fablabs-ch/wordclock/images/wiki/arduino_ide_board_selection.png

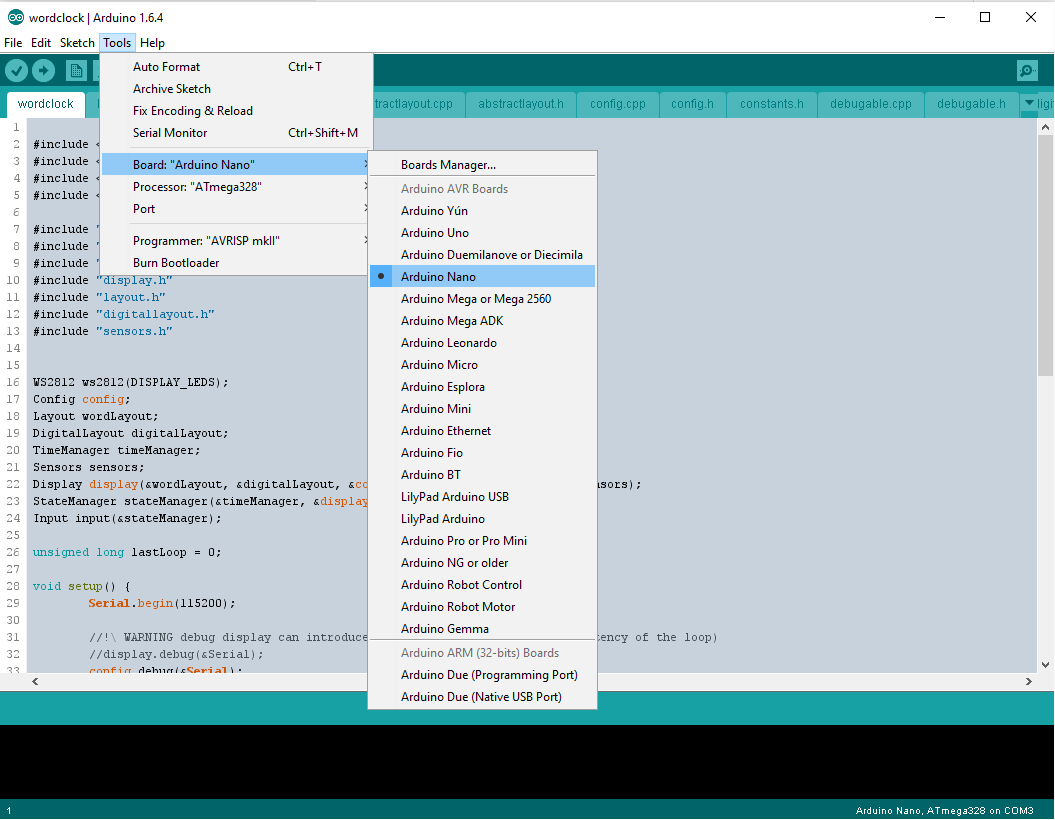
images/wiki/arduino_ide_board_selection.png
