fablabs-ch/wordclock/images/wordclockUpdatedFrench.JPG

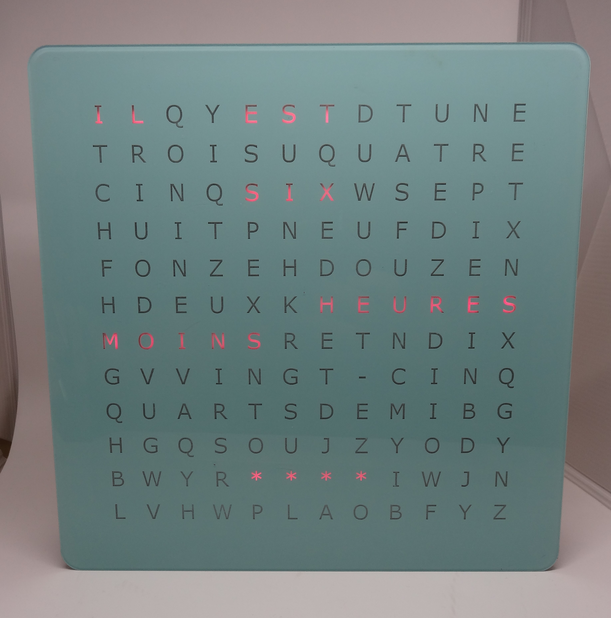
images/wordclockUpdatedFrench.JPG
