fablabs-ch/wordclock/hardware/electronic/pics/components.jpg

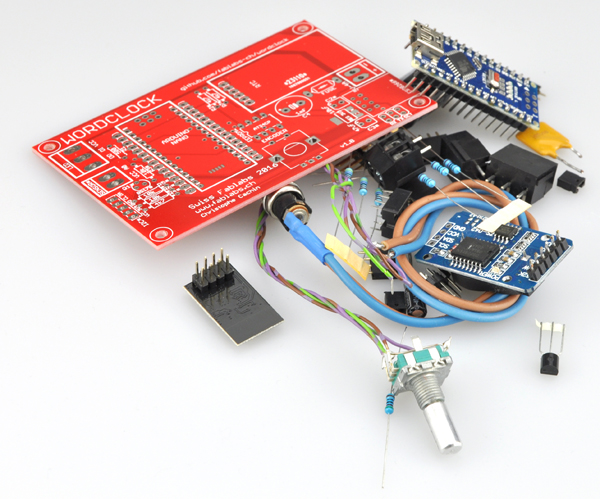
hardware/electronic/pics/components.jpg
