fablabs-ch/wordclock/hardware/box/WordClock_assembly.jpg

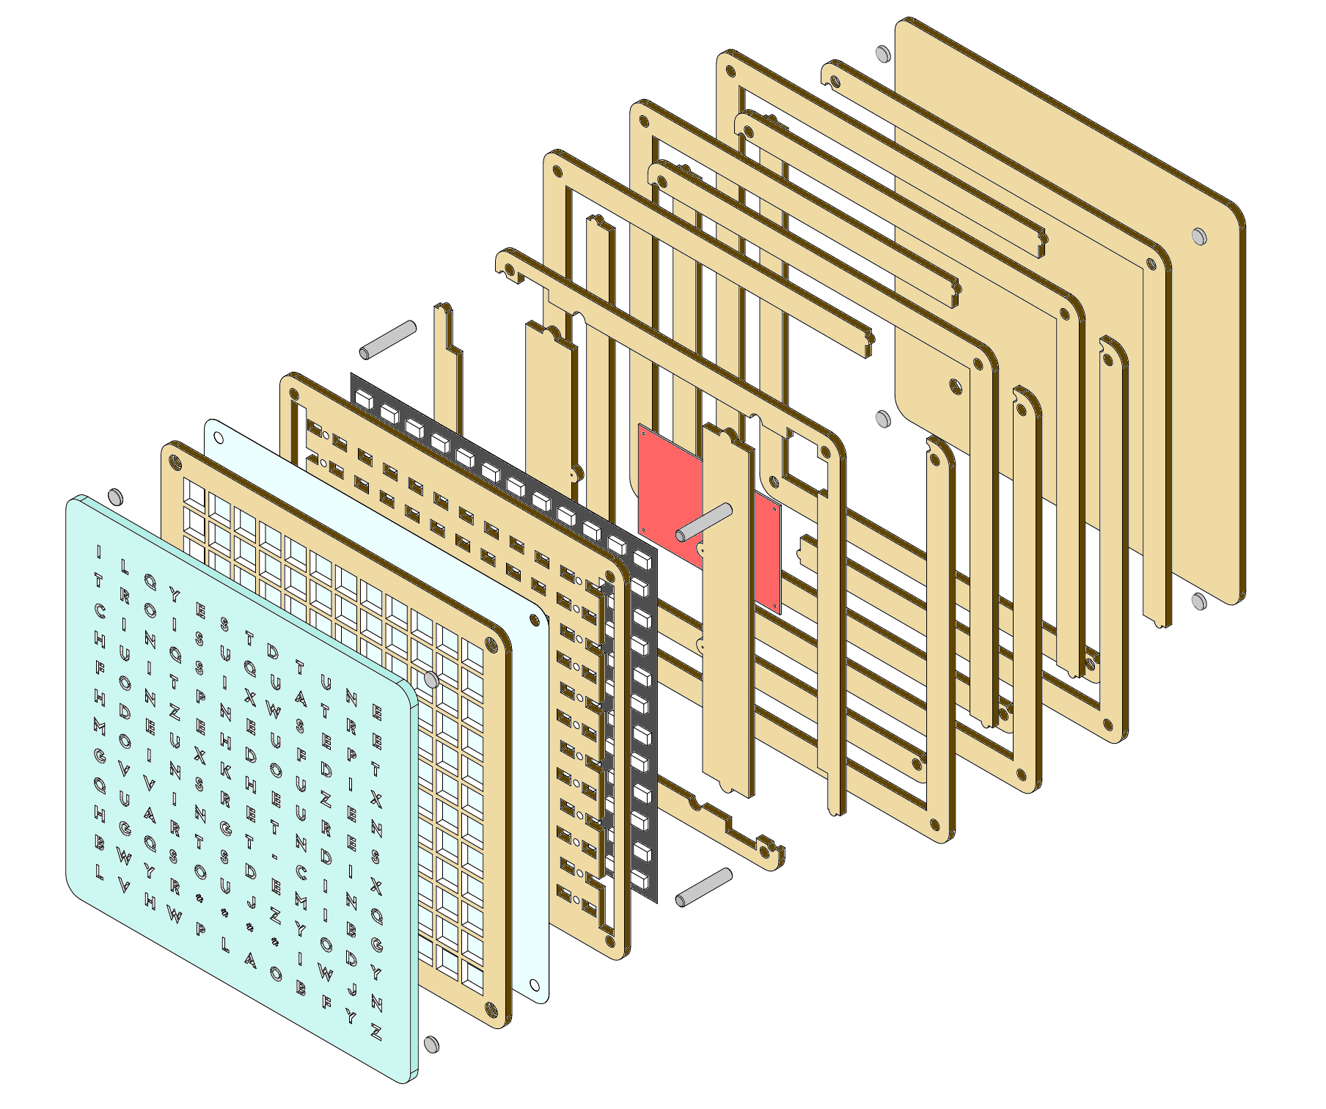
hardware/box/WordClock_assembly.jpg
