fablabs-ch/wordclock/software/wordclock/display.cpp

#include "display.h"

// #define ADD_LED(name) {int leds[] = {name};	this->addLedsOn(leds);}

Display::Display(AbstractLayout* wordLayout, AbstractLayout* digitalLayout, Config* config, TimeManager* timeManager, WS2812* ws2812, Sensors* sensors)
: wordLayout(wordLayout), digitalLayout(digitalLayout), config(config), timeManager(timeManager), leds(ws2812), sensors(sensors) {

	this->leds->setOutput(PIN_LED_STRIP);
	this->leds->setColorOrderRGB();
}

void Display::init() {
	this->draw();
	this->accNextDraw = 0;
}

void Display::loop(unsigned long dtMs) {
	this->accNextDraw += dtMs;

	bool blink = this->currentState == SET_MINUTE || this->currentState == SET_HOUR;
	if (blink) {
		int next = this->blinkOn ? 100 : 200;
		if (this->accNextDraw >= next) {
			if (this->blinkOn) {
				this->draw();
			} else {
				this->allLedsOff();
				this->writeLeds();
			}
			this->blinkOn = !this->blinkOn;
			this->accNextDraw = 0;
		}
	} else {
	    //watch for motion detection changes
	    if(this->wasMotionDetected != this->sensors->isMotionDetected()){
	        this->wasMotionDetected = this->sensors->isMotionDetected();
	        if(this->wasMotionDetected){
	            this->draw();
	        }else{
                 this->allLedsOff();
                 this->writeLeds();
            }
	    }

		if (this->accNextDraw >= DISPLAY_REFRESH_MS || this->sensors->bigChangeOccurs()) {
		    if(this->sensors->isMotionDetected()){
		        //draw only if motion is detected
			    this->draw();
		    }
			this->accNextDraw = 0;
		}
	}
}

void Display::draw() {
	uint8_t hour, minute, second;
	this->timeManager->getTime(&hour, &minute, &second);

	this->debug(hour);
	this->debug(":");
	this->debug(minute);
	this->debug(":");
	this->debug(second);
	this->debugln();

    this->computeColorOn();

	this->allLedsOff();
	if(this->currentState==CLOCK_DIGITAL || this->currentState==SET_HOUR || this->currentState==SET_MINUTE){
		this->digitalLayout->getLayout(hour, minute, second, this);
	}else{
		this->wordLayout->getLayout(hour, minute, second, this);
	}
	this->writeLeds();
}

void Display::computeColorOn(){
    hsv_type hsv = config->getColor();
    if(hsv.v==0){
        //take from sensor
        hsv.v = map(this->sensors->getLightIntensity(), 0, 255, LIGHT_MIN_AUTO, LIGHT_MAX_AUTO);
    }
	this->colorOn = this->convert(hsv);
}

void Display::matrixTester() {
	while (1) {
		cRGB colorOn = {random(255), random(255), random(255)};
		cRGB colorOff = {random(0, 15), random(0, 15), random(0, 15)};
		for (int j = 0; j < DISPLAY_LEDS; j++) {


			for (int i = 0; i < DISPLAY_LEDS; i++) {
				this->leds->set_crgb_at(i, i == j ? colorOn : colorOff);
			}
			this->leds->sync();
			delay(5);
		}
	}
}

void Display::affectLed(uint8_t led) {
	this->leds->set_crgb_at((int) led, this->colorOn);
}

void Display::setState(state_type state) {
	this->currentState = state;
	this->draw();
}

void Display::allLedsOff() {
	cRGB colorOff = {0, 0, 0};
	for (int i = 0; i < DISPLAY_LEDS; i++) {
		this->leds->set_crgb_at(i, colorOff);
	}
}

void Display::writeLeds() {
 	if (this->isDebugEnabled()) {
 	    this->displayDebug();
 	}
	this->leds->sync();
}

bool Display::isledOn(int x, int y) {
	uint16_t index = this->wordLayout->getLedIndex(x, y);

	cRGB rgb = this->leds->get_crgb_at(index);
	return rgb.r != 0 || rgb.g != 0 || rgb.b != 0;
}

cRGB Display::convert(hsv_type hsv) {
	float r = 0, g = 0, b = 0;
	float h = hsv.h, s = hsv.s, v = hsv.v;
	s /= 100;
	v /= 100;

	float t = (float) (((int) (h / 60 * 1000)) % 2000) / 1000;
	float c = v*s;
	float x = c * (1 - abs(t - 1));
	float m = v - c;

	if (h < 60) {
		r = c;
		g = x;
	} else if (h < 120) {
		r = x;
		g = c;
	} else if (h < 180) {
		g = c;
		b = x;
	} else if (h < 240) {
		g = x;
		b = c;
	} else if (h < 300) {
		r = x;
		b = c;
	} else {
		r = c;
		b = x;
	}

	return
	{
		((r + m) * 255),
				((g + m) * 255),
				((b + m) * 255)
	};
}

void Display::displayDebug() {
    this->displayDebugLine(DISPLAY_COLUMNS * 4 + 2);
    for (int col = 0; col < DISPLAY_COLUMNS; col++) {
        for (int row = 0; row < DISPLAY_ROWS; row++) {
            this->debug(" | ");
            if (this->isledOn(row, col)) {
                this->debug("*");
            } else {
                this->debug(" ");
            }
        }
        this->debug(" | ");
        this->debugln();
        this->displayDebugLine(DISPLAY_COLUMNS * 4 + 2);
    }
    this->debugln();
}

void Display::displayDebugLine(int nb) {
    for (int col = 0; col < nb; col++) {
        this->debug("-");
    }
    this->debugln();
}
